robouden/bGeigieNano/assembly/bGeigieNano_car_mount.jpg

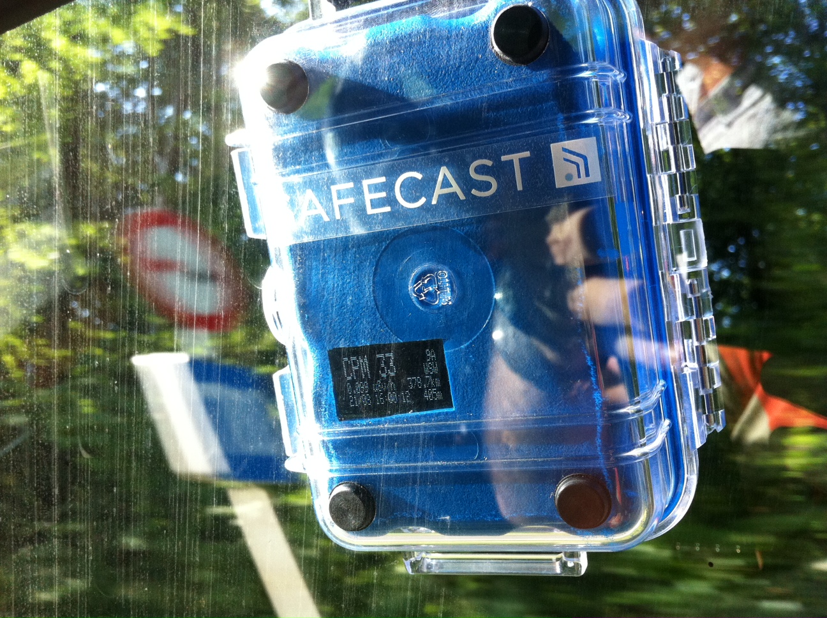
assembly/bGeigieNano_car_mount.jpg
