robouden/bGeigieNano/assembly/bGeigieNanoKit_bb_600.jpg

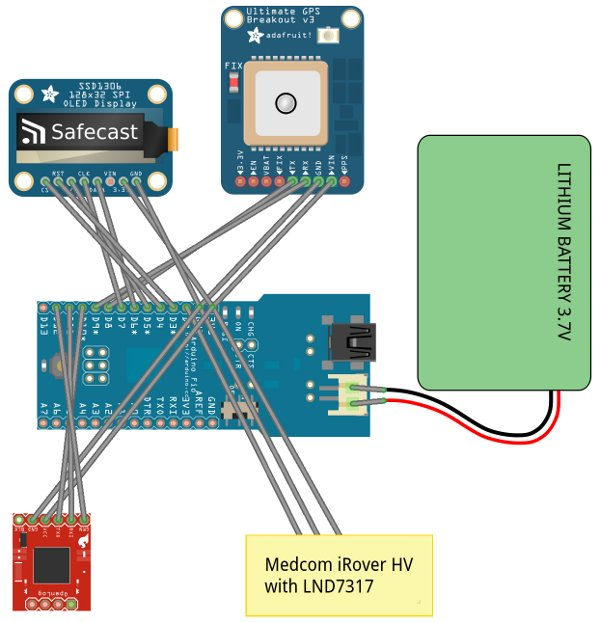
assembly/bGeigieNanoKit_bb_600.jpg
