robouden/bGeigieNano/assembly/bGeigieNanoKit_sheet.png

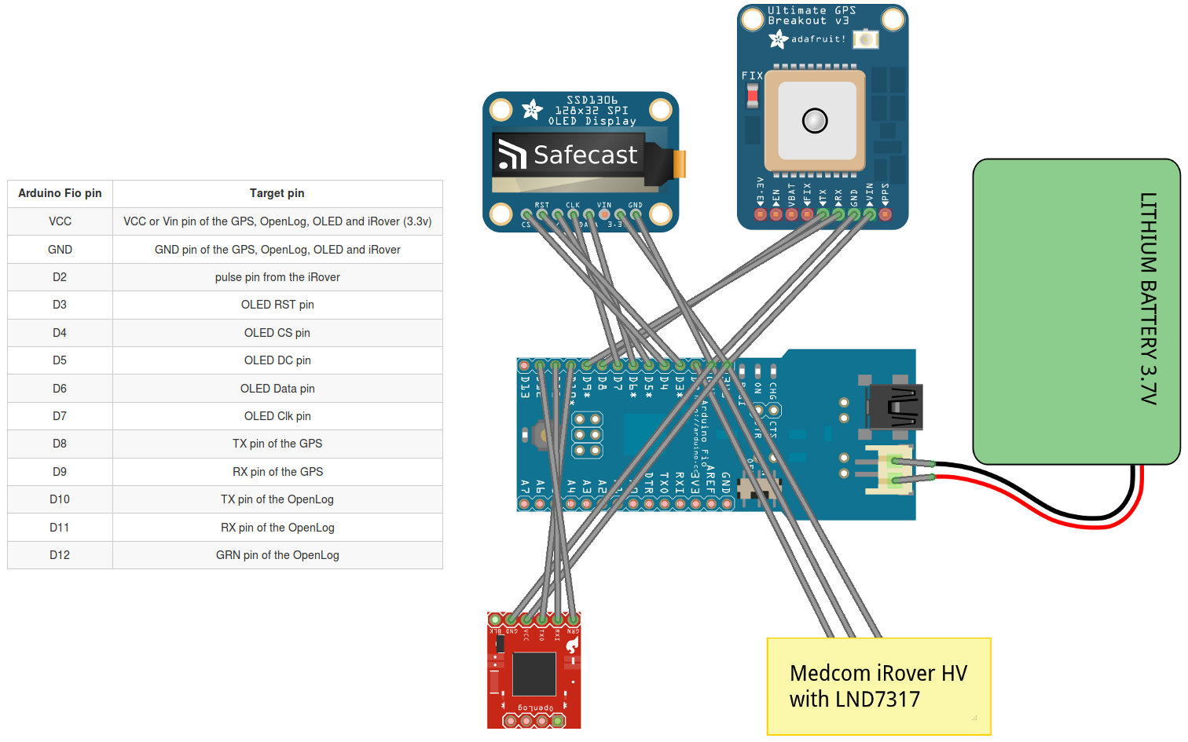
assembly/bGeigieNanoKit_sheet.png
